Christian-Me/healthy-indoors-project/docs/sensors/MHZ19/dimensions.bmp

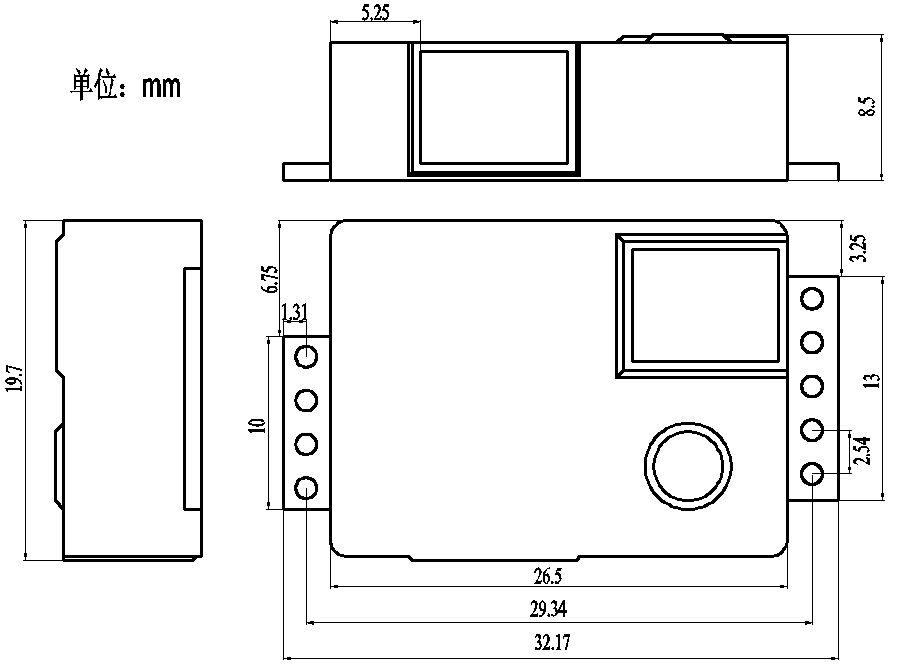
docs/sensors/MHZ19/dimensions.bmp
