Christian-Me/healthy-indoors-project/graphics/hue.png

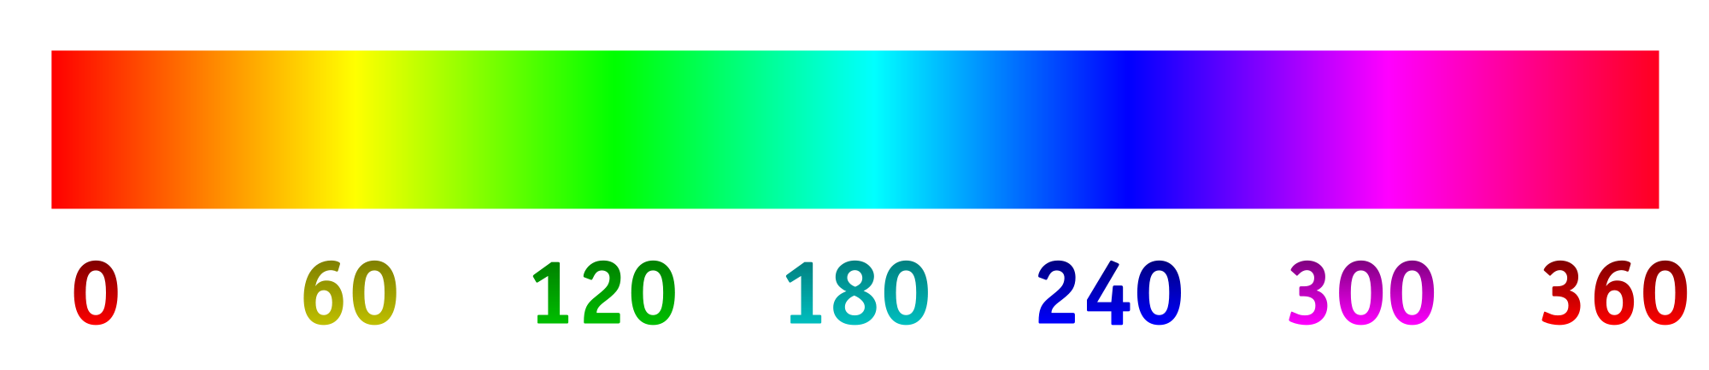
graphics/hue.png
