Christian-Me/healthy-indoors-project/graphics/temp-humidity-influenca.jpg

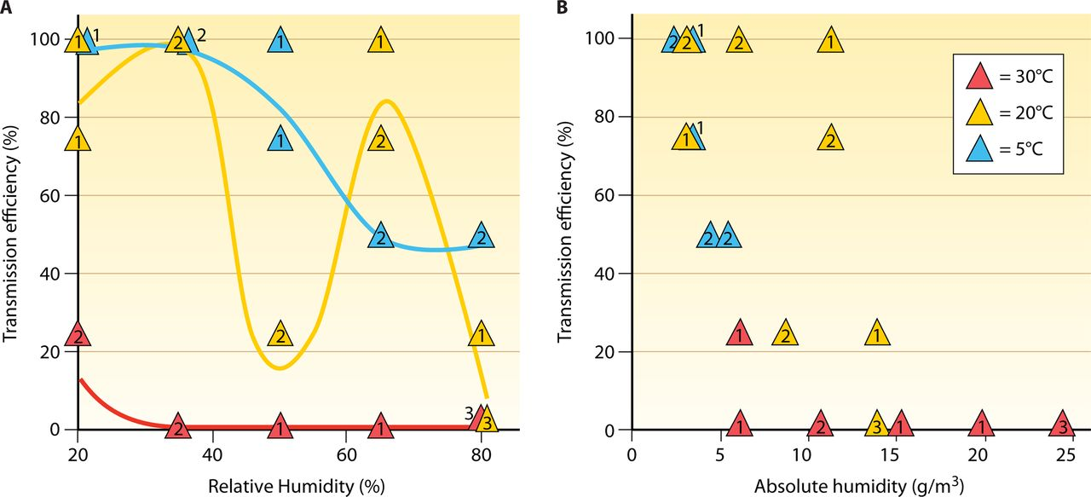
graphics/temp-humidity-influenca.jpg
