Christian-Me/healthy-indoors-project/3d-print/components/6-2mm-button-switch-1/untitled.173.jpg

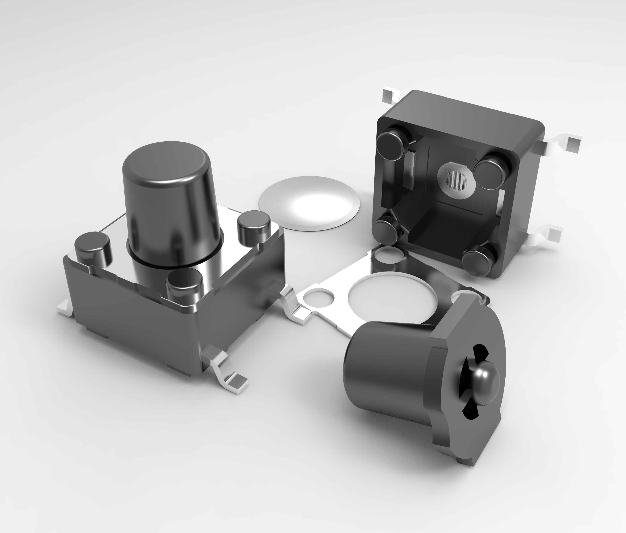
3d-print/components/6-2mm-button-switch-1/untitled.173.jpg
