Christian-Me/healthy-indoors-project/3d-print/components/cjmcu-680-bme680-bosch-sensor/CJMCU-680.png

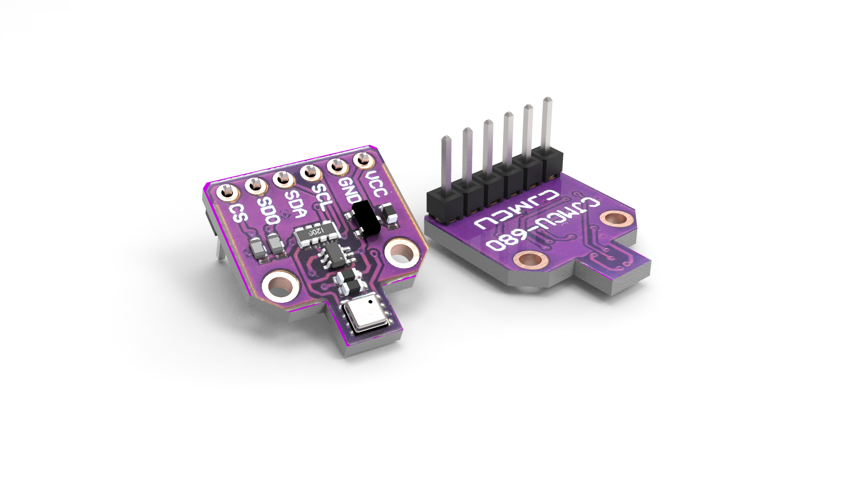
3d-print/components/cjmcu-680-bme680-bosch-sensor/CJMCU-680.png
