Christian-Me/healthy-indoors-project/3d-print/components/mh-z19-module-1/Capture.JPG

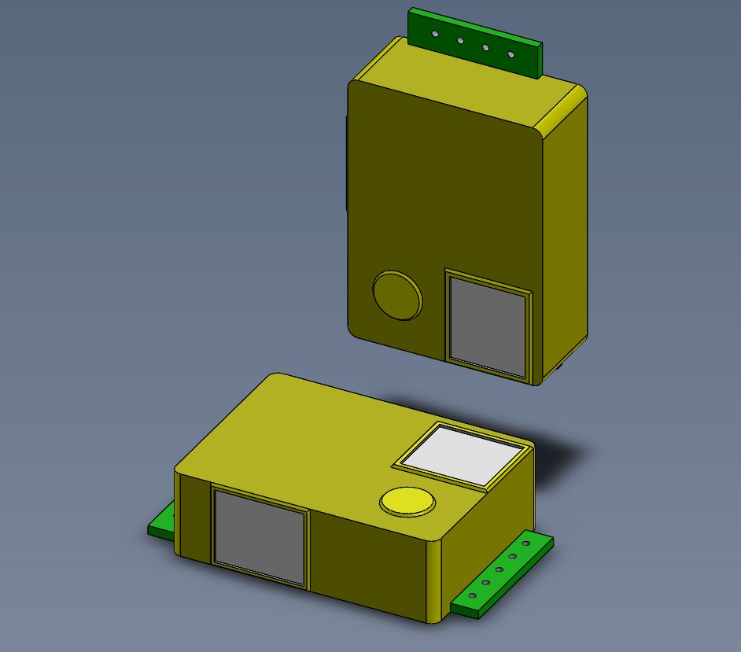
3d-print/components/mh-z19-module-1/Capture.JPG
