Christian-Me/healthy-indoors-project/3d-print/components/neopixel-stick-8-x-ws2812-5050-rgb-led/Capture.JPG

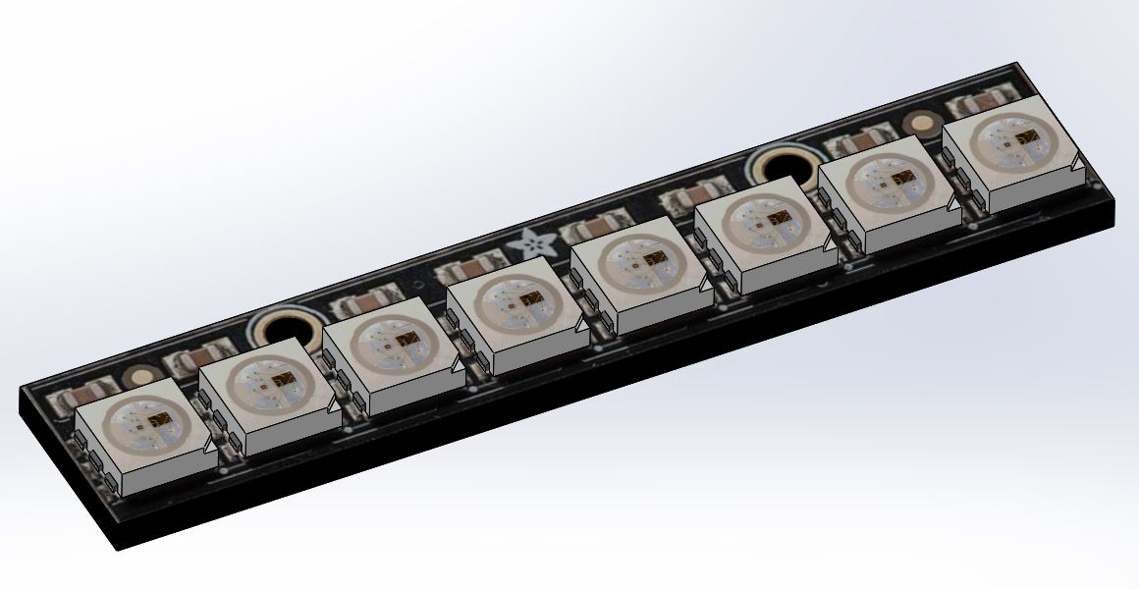
3d-print/components/neopixel-stick-8-x-ws2812-5050-rgb-led/Capture.JPG
