Christian-Me/healthy-indoors-project/3d-print/components/neopixel-stick-8-x-ws2812-5050-rgb-led/LED - SMD RGB (WS2812) - Front.jpg

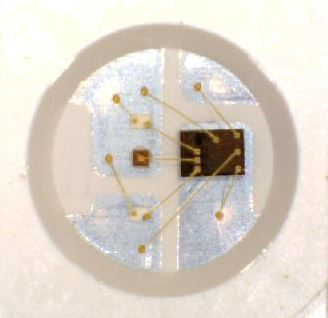
3d-print/components/neopixel-stick-8-x-ws2812-5050-rgb-led/LED - SMD RGB (WS2812) - Front.jpg
