Christian-Me/healthy-indoors-project/3d-print/components/sw2812b-8/LED WS2812B-8/1fafdf11-416a-4e42-9cf1-738db5bde44c.PNG

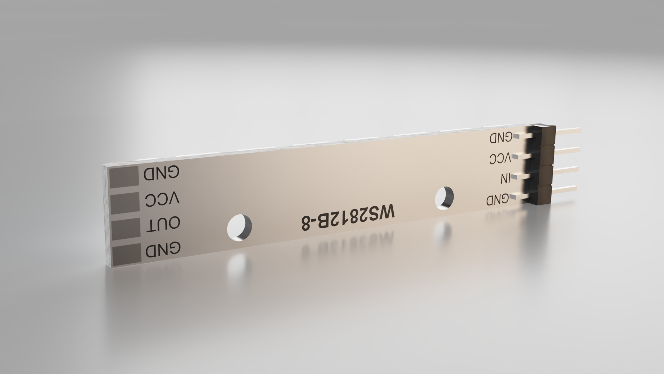
3d-print/components/sw2812b-8/LED WS2812B-8/1fafdf11-416a-4e42-9cf1-738db5bde44c.PNG
