Christian-Me/healthy-indoors-project/3d-print/components/sw2812b-8/LED WS2812B-8/WS2812B-8_2019-Jun-21_11-59-07AM-000_CustomizedView14946539427.png

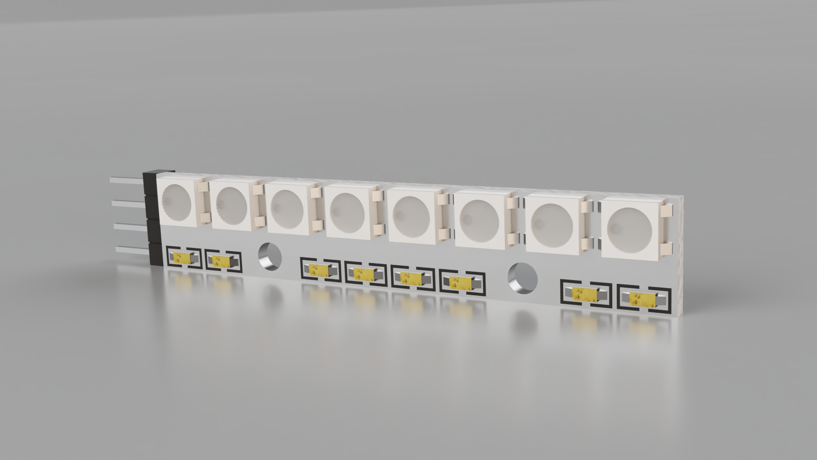
3d-print/components/sw2812b-8/LED WS2812B-8/WS2812B-8_2019-Jun-21_11-59-07AM-000_CustomizedView14946539427.png
