Christian-Me/healthy-indoors-project/3d-print/components/ws2812b-rgb-led-adafruit-neopixel-1/Renderings/2812 view 2.PNG

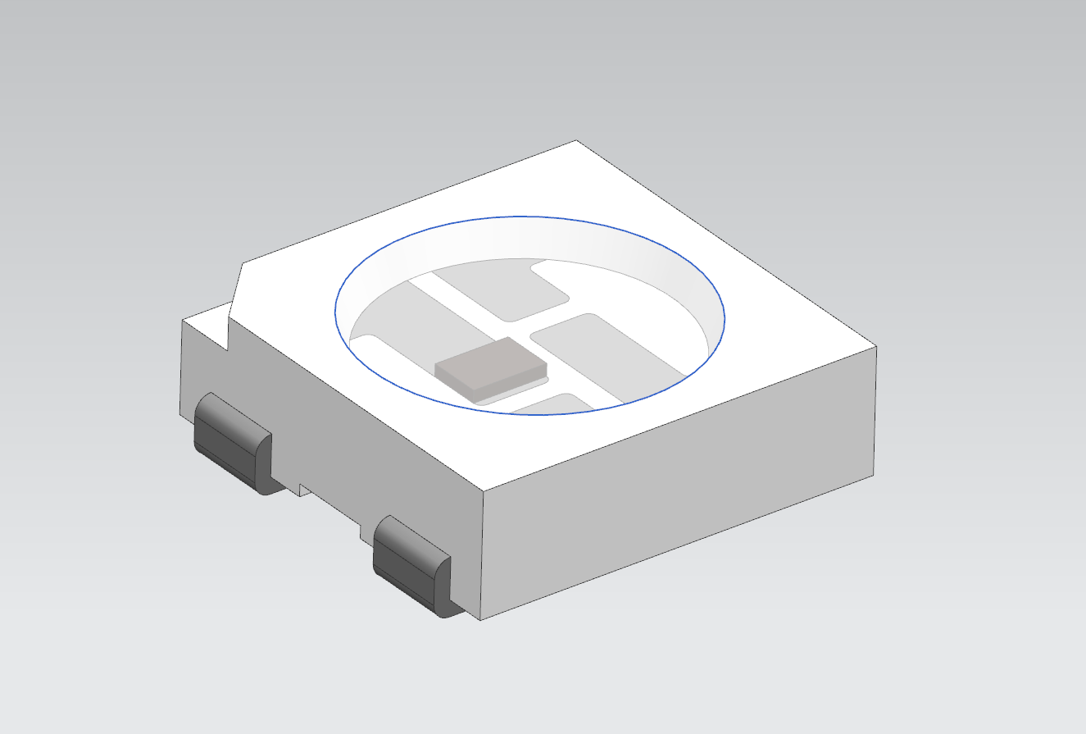
3d-print/components/ws2812b-rgb-led-adafruit-neopixel-1/Renderings/2812 view 2.PNG
