Christian-Me/healthy-indoors-project/3d-print/components/ws2812b-rgb-led-adafruit-neopixel-1/Renderings/View 8.PNG

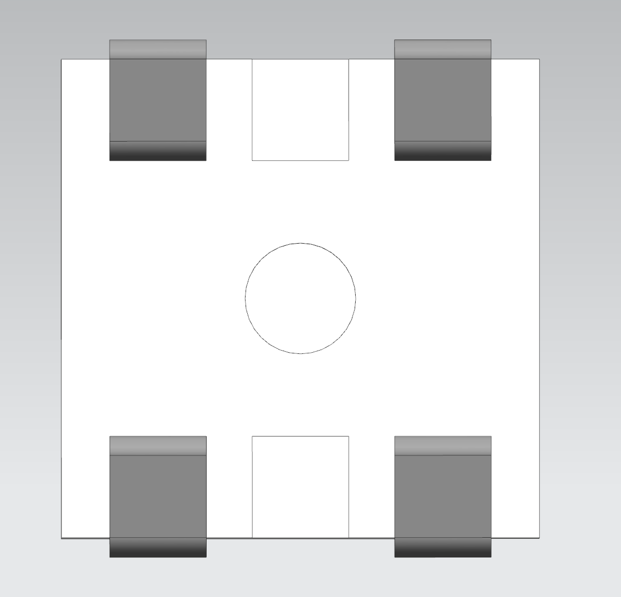
3d-print/components/ws2812b-rgb-led-adafruit-neopixel-1/Renderings/View 8.PNG
