Christian-Me/healthy-indoors-project/3d-print/components/ws2812b-rgb-led-adafruit-neopixel-1/Renderings/View 9.PNG

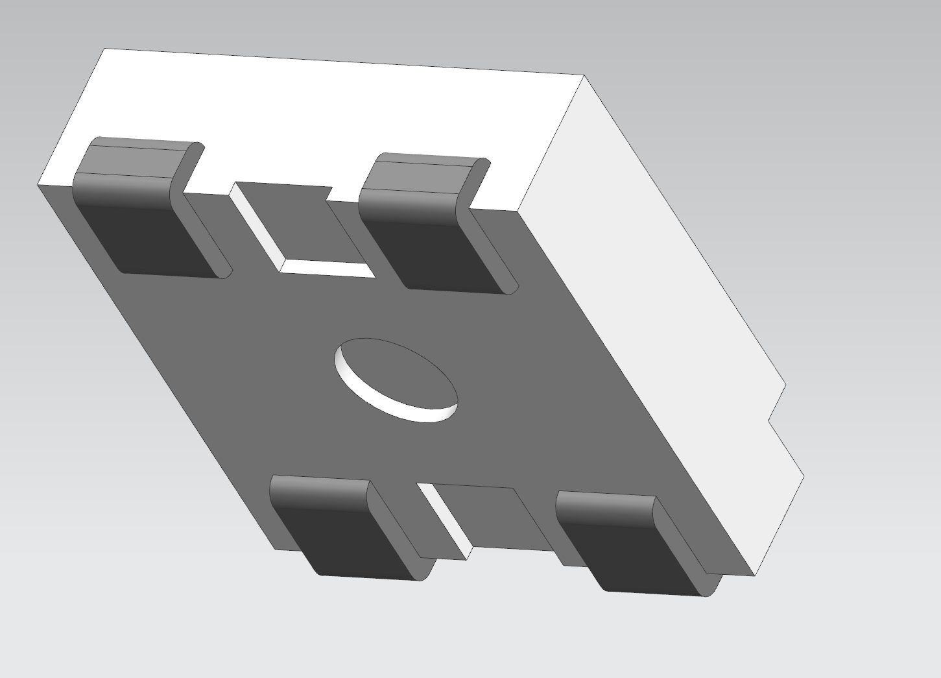
3d-print/components/ws2812b-rgb-led-adafruit-neopixel-1/Renderings/View 9.PNG
