Christian-Me/healthy-indoors-project/3d-print/components/wemos-d1-mini-2.x/SOIC_16_ch340.SLDPRT

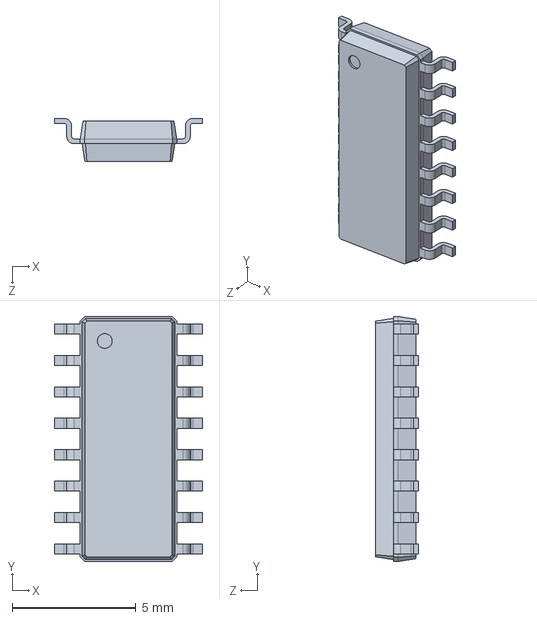
[picture p48: CAD file, 2020-10-18]
3d-print/components/wemos-d1-mini-2.x/SOIC_16_ch340.SLDPRT
6.00 x 9.90 x 1.75 mm
