Christian-Me/healthy-indoors-project/3d-print/components/wemos-d1-mini-2.x/WEMOS-D1-mini_detailed.SLDPRT

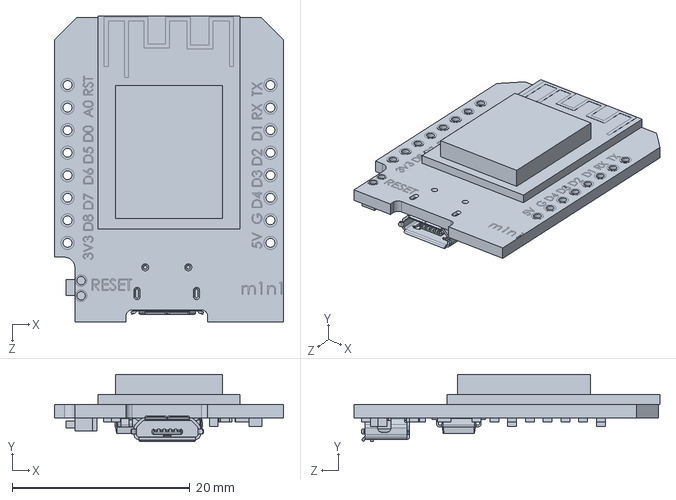
[picture p49: CAD file, 2020-10-18]
3d-print/components/wemos-d1-mini-2.x/WEMOS-D1-mini_detailed.SLDPRT
25.8 x 7.60 x 34.4 mm
