Christian-Me/healthy-indoors-project/3d-print/stl/top.stl

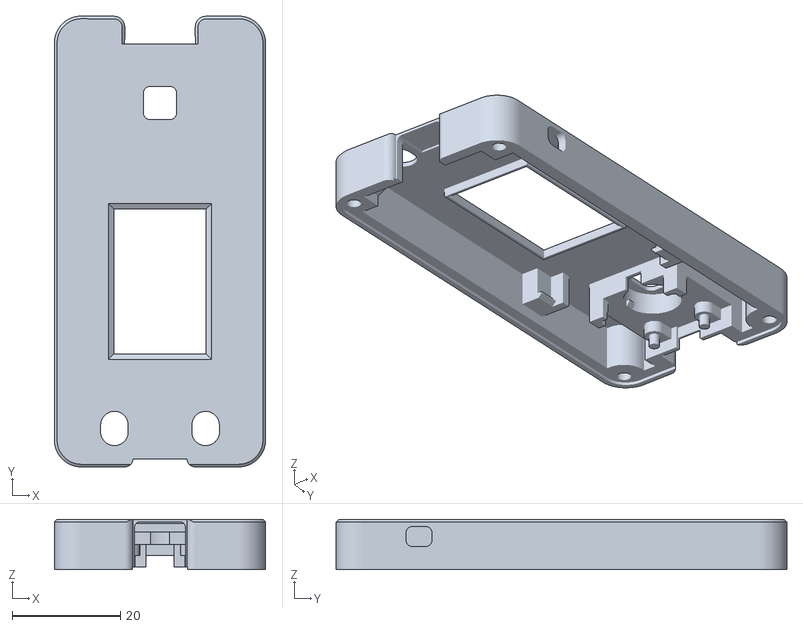
[picture p51: CAD file, 2020-10-18]
3d-print/stl/top.stl
39.0 x 83.3 x 9.30
