Christian-Me/healthy-indoors-project/3d-print/components/wemos-d1-mini-2.x/Pin_header_str_1x08_p2_54mm.sldprt

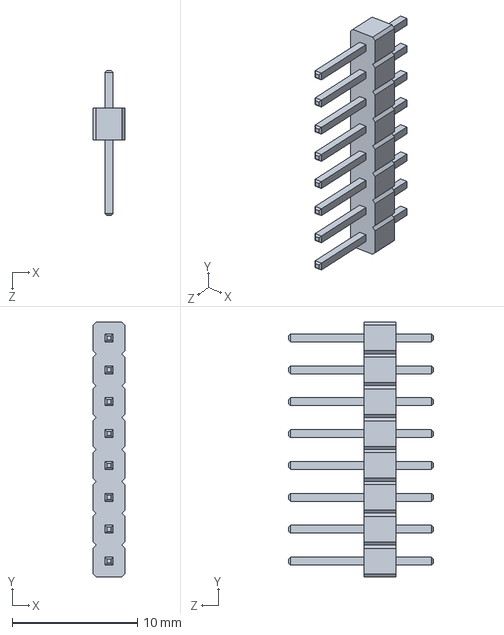
[picture p52: CAD file, 2020-10-18]
3d-print/components/wemos-d1-mini-2.x/Pin_header_str_1x08_p2_54mm.sldprt
2.54 x 20.3 x 11.5 mm
