Christian-Me/healthy-indoors-project/3d-print/stl/wemos-bme680-top.stl

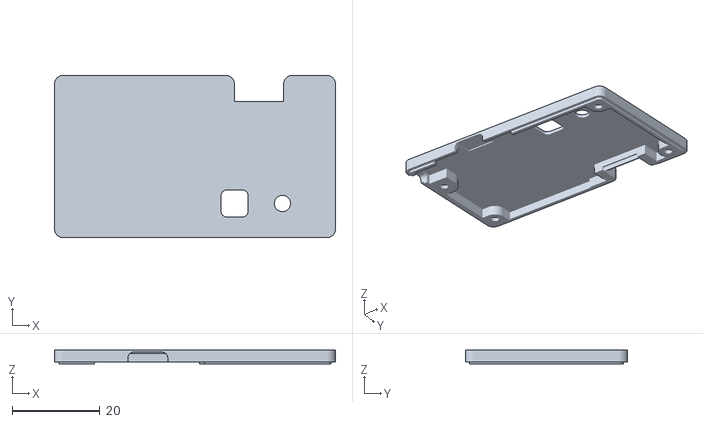
[picture p53: CAD file, 2020-10-18]
3d-print/stl/wemos-bme680-top.stl
64.0 x 37.0 x 3.30
