Christian-Me/healthy-indoors-project/3d-print/stl/wemos-2.x-bme680-top-white.stl

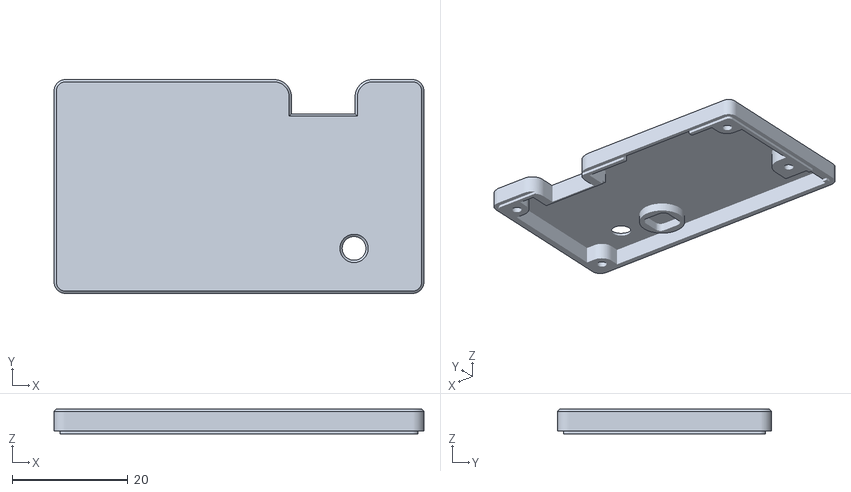
[picture p54: CAD file, 2020-10-18]
3d-print/stl/wemos-2.x-bme680-top-white.stl
64.0 x 37.0 x 4.30
