Christian-Me/healthy-indoors-project/3d-print/stl/wemos-bme680-bottom.stl

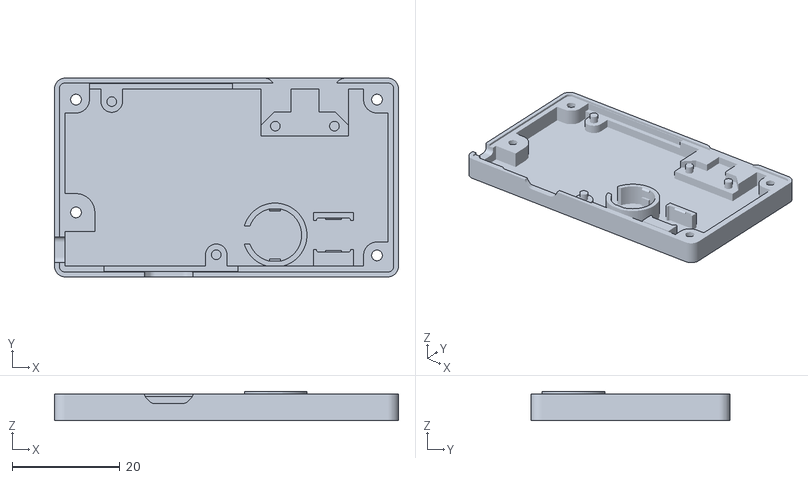
[picture p55: CAD file, 2020-10-18]
3d-print/stl/wemos-bme680-bottom.stl
64.0 x 37.0 x 5.41
