Christian-Me/healthy-indoors-project/images/William_Farr's_name_on_the_Frieze_of_the_LSHTM_building_.jpg

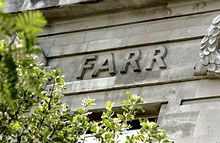
images/William_Farr's_name_on_the_Frieze_of_the_LSHTM_building_.jpg
